DigiTorus86/ESP32-R4ge-Pro/PlatformIO/esp32-r4ge-pro-tombstone/include/boop_wav.h

const PROGMEM unsigned char boop_wav[6360] = {
  0x52, 0x49, 0x46, 0x46, 0xd0, 0x18, 0x00, 0x00, 0x57, 0x41, 0x56, 0x45,
  0x66, 0x6d, 0x74, 0x20, 0x10, 0x00, 0x00, 0x00, 0x01, 0x00, 0x01, 0x00,
  0x11, 0x2b, 0x00, 0x00, 0x22, 0x56, 0x00, 0x00, 0x02, 0x00, 0x10, 0x00,
  0x64, 0x61, 0x74, 0x61, 0xac, 0x18, 0x00, 0x00, 0x01, 0x00, 0xfe, 0xff,
  0x03, 0x00, 0xfb, 0xff, 0x06, 0x00, 0xfa, 0xff, 0x06, 0x00, 0xfb, 0xff,
  0x03, 0x00, 0xfe, 0xff, 0x01, 0x00, 0xff, 0xff, 0x02, 0x00, 0xfe, 0xff,
  0x01, 0x00, 0x00, 0x00, 0xff, 0xff, 0x01, 0x00, 0x00, 0x00, 0xff, 0xff,
  0x02, 0x00, 0xfe, 0xff, 0x01, 0x00, 0x00, 0x00, 0xff, 0xff, 0x02, 0x00,
  0xfe, 0xff, 0x01, 0x00, 0x00, 0x00, 0x00, 0x00, 0xff, 0xff, 0x03, 0x00,
  0xfb, 0xff, 0x05, 0x00, 0xfd, 0xff, 0x00, 0x00, 0x03, 0x00, 0xfb, 0xff,
  0x05, 0x00, 0xfc, 0xff, 0x02, 0x00, 0x00, 0x00, 0xff, 0xff, 0x01, 0x00,
  0xff, 0xff, 0x00, 0x00, 0x02, 0x00, 0xfc, 0xff, 0x05, 0x00, 0xfc, 0xff,
  0x03, 0x00, 0xfd, 0xff, 0x03, 0x00, 0xfc, 0xff, 0x06, 0x00, 0xfa, 0xff,
  0x03, 0x00, 0x00, 0x00, 0xfe, 0xff, 0x03, 0x00, 0xfd, 0xff, 0x02, 0x00,
  0xff, 0xff, 0x01, 0x00, 0xfe, 0xff, 0x03, 0x00, 0xfd, 0xff, 0x03, 0x00,
  0xfc, 0xff, 0x05, 0x00, 0xfb, 0xff, 0x05, 0x00, 0xfb, 0xff, 0x04, 0x00,
  0xfd, 0xff, 0x02, 0x00, 0xff, 0xff, 0x01, 0x00, 0xff, 0xff, 0x01, 0x00,
  0xff, 0xff, 0x00, 0x00, 0x01, 0x00, 0xff, 0xff, 0x00, 0x00, 0x01, 0x00,
  0xff, 0xff, 0x00, 0x00, 0x01, 0x00, 0xfe, 0xff, 0x02, 0x00, 0xff, 0xff,
  0x00, 0x00, 0x00, 0x00, 0x01, 0x00, 0xfe, 0xff, 0x02, 0x00, 0xfe, 0xff,
  0x02, 0x00, 0xfe, 0xff, 0x03, 0x00, 0xfc, 0xff, 0x04, 0x00, 0xfd, 0xff,
  0x01, 0x00, 0x01, 0x00, 0xff, 0xff, 0x00, 0x00, 0x00, 0x00, 0x00, 0x00,
  0x00, 0x00, 0x01, 0x00, 0xfe, 0xff, 0x02, 0x00, 0xfe, 0xff, 0x02, 0x00,
  0xfe, 0xff, 0x03, 0x00, 0xfc, 0xff, 0x04, 0x00, 0xfc, 0xff, 0x04, 0x00,
  0xfd, 0xff, 0x01, 0x00, 0x00, 0x00, 0x00, 0x00, 0x01, 0x00, 0xfe, 0xff,
  0x01, 0x00, 0x00, 0x00, 0x00, 0x00, 0x00, 0x00, 0x00, 0x00, 0xff, 0xff,
  0x02, 0x00, 0xfe, 0xff, 0x02, 0x00, 0xfe, 0xff, 0x02, 0x00, 0xfe, 0xff,
  0x02, 0x00, 0xff, 0xff, 0x00, 0x00, 0x01, 0x00, 0xff, 0xff, 0x00, 0x00,
  0x01, 0x00, 0xfe, 0xff, 0x03, 0x00, 0xfc, 0xff, 0x03, 0x00, 0xff, 0xff,
  0x00, 0x00, 0x01, 0x00, 0xfd, 0xff, 0x03, 0x00, 0xfe, 0xff, 0x02, 0x00,
  0xff, 0xff, 0x00, 0x00, 0xff, 0xff, 0x01, 0x00, 0x00, 0x00, 0x00, 0x00,
  0x00, 0x00, 0xff, 0xff, 0x01, 0x00, 0xff, 0xff, 0x02, 0x00, 0xfe, 0xff,
  0x01, 0x00, 0x00, 0x00, 0x00, 0x00, 0x00, 0x00, 0x00, 0x00, 0x00, 0x00,
  0x00, 0x00, 0x00, 0x00, 0x01, 0x00, 0xfd, 0xff, 0x04, 0x00, 0xfc, 0xff,
  0x04, 0x00, 0xfd, 0xff, 0x01, 0x00, 0x01, 0x00, 0xfe, 0xff, 0x02, 0x00,
  0xff, 0xff, 0x01, 0x00, 0xfe, 0xff, 0x03, 0x00, 0xfc, 0xff, 0x05, 0x00,
  0xfb, 0xff, 0x03, 0x00, 0xff, 0xff, 0x00, 0x00, 0x01, 0x00, 0xff, 0xff,
  0x00, 0x00, 0x00, 0x00, 0x01, 0x00, 0xfe, 0xff, 0x03, 0x00, 0xfd, 0xff,
  0x02, 0x00, 0xfe, 0xff, 0x03, 0x00, 0xfc, 0xff, 0x04, 0x00, 0xfd, 0xff,
  0x02, 0x00, 0xff, 0xff, 0x01, 0x00, 0xfe, 0xff, 0x03, 0x00, 0xfd, 0xff,
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
};
