DigiTorus86/ESP32-R4ge-Pro/PlatformIO/esp32-r4ge-pro-gravitack/include/explosion_wav.h

const PROGMEM unsigned char explosion_wav[5775] = { 
	0x52, 0x49, 0x46, 0x46, 0x87, 0x16, 0x00, 0x00, 0x57, 0x41, 0x56, 0x45,
	0x66, 0x6D, 0x74, 0x20, 0x10, 0x00, 0x00, 0x00, 0x01, 0x00, 0x01, 0x00,
	0x11, 0x2B, 0x00, 0x00, 0x11, 0x2B, 0x00, 0x00, 0x01, 0x00, 0x08, 0x00,
	0x64, 0x61, 0x74, 0x61, 0x63, 0x16, 0x00, 0x00, 0x80, 0x80, 0x80, 0x80,
	0x7F, 0x7E, 0x7D, 0x7C, 0x7B, 0x7B, 0x7A, 0x7A, 0x7D, 0x7F, 0x7F, 0x81,
	0x84, 0x88, 0x8A, 0x88, 0x88, 0x91, 0x9A, 0x9B, 0x9B, 0x9B, 0x9C, 0x9A,
	0x9B, 0x9E, 0xA5, 0xA8, 0xA1, 0x9F, 0xA5, 0xA5, 0x9A, 0x96, 0x93, 0x94,
	0x96, 0x90, 0x8B, 0x84, 0x7C, 0x7A, 0x7B, 0x78, 0x6F, 0x62, 0x54, 0x4D,
	0x4A, 0x4C, 0x51, 0x56, 0x5A, 0x5F, 0x63, 0x68, 0x6E, 0x76, 0x84, 0x96,
	0xA6, 0xB0, 0xB9, 0xC4, 0xD1, 0xD0, 0xCA, 0xC3, 0xBA, 0xB1, 0xA8, 0xA0,
	0x98, 0x92, 0x89, 0x7A, 0x72, 0x77, 0x73, 0x6A, 0x69, 0x60, 0x49, 0x41,
	0x44, 0x44, 0x40, 0x37, 0x33, 0x32, 0x35, 0x3A, 0x3E, 0x47, 0x52, 0x5C,
	0x66, 0x6E, 0x76, 0x7D, 0x84, 0x8D, 0xA4, 0xAF, 0xB4, 0xB8, 0xBC, 0xC8,
	0xCC, 0xCD, 0xD8, 0xF7, 0xFE, 0xF7, 0xFA, 0xF4, 0xE1, 0xD0, 0xC7, 0xCB,
	0xC6, 0xB6, 0xA4, 0x92, 0x83, 0x75, 0x69, 0x5C, 0x4E, 0x3D, 0x29, 0x1A,
	0x0F, 0x08, 0x08, 0x07, 0x07, 0x07, 0x08, 0x0A, 0x1B, 0x30, 0x30, 0x11,
	0x0E, 0x21, 0x20, 0x2F, 0x35, 0x33, 0x3C, 0x43, 0x44, 0x4A, 0x48, 0x45,
	0x46, 0x44, 0x40, 0x43, 0x4F, 0x56, 0x50, 0x44, 0x49, 0x50, 0x54, 0x58,
	0x5F, 0x68, 0x6F, 0x76, 0x7C, 0x86, 0x9A, 0xB2, 0xC0, 0xCE, 0xDF, 0xE4,
	0xE4, 0xE1, 0xDA, 0xD4, 0xCA, 0xBD, 0xB0, 0xA6, 0x9C, 0x93, 0x8C, 0x85,
	0x80, 0x7C, 0x77, 0x74, 0x6F, 0x6B, 0x6A, 0x69, 0x67, 0x66, 0x66, 0x66,
	0x64, 0x5F, 0x5C, 0x5E, 0x5F, 0x52, 0x4B, 0x49, 0x3C, 0x31, 0x36, 0x3B,
	0x3D, 0x47, 0x51, 0x64, 0x7A, 0x85, 0x93, 0xA2, 0xA1, 0x9F, 0xA5, 0xA3,
	0x9F, 0xA9, 0xB1, 0xB2, 0xB6, 0xB5, 0xB7, 0xBB, 0xBE, 0xC8, 0xE1, 0xEE,
	0xE4, 0xE3, 0xE7, 0xEB, 0xF2, 0xFC, 0xFA, 0xEE, 0xE5, 0xD7, 0xBF, 0xB5,
	0xB6, 0xB8, 0xB9, 0xBC, 0xBE, 0xBF, 0xB4, 0xA8, 0x9B, 0x81, 0x87, 0x9D,
	0x97, 0x85, 0x81, 0x80, 0x7D, 0x7C, 0x86, 0x7C, 0x75, 0x7A, 0x73, 0x6A,
	0x62, 0x5C, 0x56, 0x51, 0x4C, 0x49, 0x46, 0x43, 0x40, 0x3C, 0x3D, 0x3D,
	0x37, 0x2B, 0x1C, 0x12, 0x17, 0x1C, 0x0C, 0x09, 0x1C, 0x22, 0x29, 0x31,
	0x3E, 0x45, 0x49, 0x5E, 0x6A, 0x71, 0x74, 0x74, 0x73, 0x81, 0x8E, 0xA6,
	0xC5, 0xBF, 0xC1, 0xC8, 0xCB, 0xC4, 0xB8, 0xB5, 0xBD, 0xBF, 0xBA, 0xB6,
	0xB0, 0xAC, 0xB2, 0xB9, 0xAE, 0xA8, 0xA5, 0xAA, 0xB0, 0xAA, 0x8E, 0x86,
	0x8E, 0x8E, 0x93, 0xA4, 0xAA, 0x9D, 0x7F, 0x58, 0x48, 0x51, 0x5C, 0x59,
	0x61, 0x4F, 0x46, 0x4E, 0x47, 0x41, 0x4B, 0x4A, 0x4D, 0x5E, 0x60, 0x6F,
	0x79, 0x85, 0x93, 0xAB, 0xB8, 0xB9, 0xB1, 0xA8, 0xA8, 0xA6, 0xA6, 0x9E,
	0x9E, 0xA6, 0xA0, 0x96, 0x99, 0x9E, 0xA0, 0xA3, 0xA6, 0x9A, 0x82, 0x6C,
	0x69, 0x74, 0x88, 0xA1, 0xA3, 0x93, 0x74, 0x55, 0x49, 0x4A, 0x66, 0x8F,
	0x9B, 0x70, 0x56, 0x58, 0x5A, 0x57, 0x50, 0x54, 0x5D, 0x6D, 0x78, 0x81,
	0x84, 0x8A, 0x87, 0x90, 0x92, 0x8C, 0x91, 0x9B, 0xAC, 0xA9, 0x9E, 0xA3,
	0xA5, 0xA4, 0xAB, 0xBC, 0xC8, 0xC1, 0xAF, 0xAF, 0xB6, 0x97, 0x9E, 0xAC,
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
};
