DigiTorus86/ESP32-R4ge-Pro/PlatformIO/esp32-r4ge-pro-gravitack/include/fire_wav.h

const PROGMEM unsigned char fire_wav[3431] = { 
	0x52, 0x49, 0x46, 0x46, 0x5F, 0x0D, 0x00, 0x00, 0x57, 0x41, 0x56, 0x45,
	0x66, 0x6D, 0x74, 0x20, 0x10, 0x00, 0x00, 0x00, 0x01, 0x00, 0x01, 0x00,
	0x11, 0x2B, 0x00, 0x00, 0x11, 0x2B, 0x00, 0x00, 0x01, 0x00, 0x08, 0x00,
	0x64, 0x61, 0x74, 0x61, 0x3B, 0x0D, 0x00, 0x00, 0x7F, 0x80, 0x7F, 0x80,
	0x7E, 0x81, 0x7D, 0x7F, 0x7E, 0x83, 0x84, 0x95, 0x96, 0x76, 0x68, 0x60,
	0x6A, 0x67, 0x76, 0x71, 0x85, 0x7D, 0xA2, 0x95, 0x7B, 0x94, 0x90, 0xBE,
	0x92, 0x91, 0xC1, 0xA3, 0x96, 0x7B, 0x8D, 0xAA, 0x7D, 0x78, 0x60, 0x8A,
	0x77, 0x46, 0x41, 0x4A, 0x76, 0x36, 0x36, 0x43, 0x70, 0x80, 0x49, 0x51,
	0x69, 0x82, 0x68, 0x5A, 0x5C, 0xA3, 0x92, 0x9D, 0xAA, 0x84, 0xD1, 0xA2,
	0x97, 0xC3, 0x92, 0x96, 0xA8, 0x8A, 0xAC, 0xCF, 0xCB, 0xA2, 0xA0, 0x97,
	0xC6, 0xC3, 0xAF, 0xB2, 0x9D, 0xD3, 0x9B, 0x6A, 0x73, 0x70, 0x58, 0x79,
	0x63, 0x41, 0x5D, 0x74, 0x57, 0x23, 0x12, 0x29, 0x46, 0x3E, 0x55, 0x5A,
	0x52, 0x5F, 0x6C, 0x38, 0x34, 0x40, 0x87, 0xA0, 0x6D, 0x82, 0x7E, 0xB5,
	0xB8, 0x7F, 0x8E, 0xA8, 0x84, 0x9C, 0xBE, 0xB2, 0x93, 0xA0, 0xCC, 0xC8,
	0xC5, 0x95, 0x97, 0xA5, 0xAA, 0x6E, 0x7A, 0xB0, 0x9F, 0xB7, 0x92, 0x85,
	0x77, 0x5F, 0x5E, 0x4D, 0x7D, 0x78, 0x74, 0x85, 0xA3, 0xAA, 0x39, 0x22,
	0x37, 0x53, 0x63, 0x78, 0x7B, 0x9B, 0x8B, 0x29, 0x50, 0x62, 0x4D, 0x3F,
	0x58, 0x8D, 0x93, 0x94, 0x76, 0x7C, 0x77, 0x5B, 0x67, 0x6E, 0xA5, 0x80,
	0x87, 0x96, 0xA7, 0x82, 0x55, 0x82, 0x80, 0x75, 0x99, 0xCC, 0x96, 0x82,
	0x72, 0x95, 0x72, 0x82, 0xA6, 0xAA, 0x83, 0x94, 0xA5, 0x9C, 0xA0, 0x79,
	0x8B, 0x5E, 0x8D, 0x9B, 0xB2, 0x9D, 0x96, 0x62, 0x7A, 0x8C, 0x56, 0x76,
	0x84, 0x82, 0x78, 0xA6, 0x8B, 0xB1, 0x92, 0x72, 0x77, 0x76, 0x89, 0xA5,
	0xDA, 0xAA, 0x91, 0x8E, 0x68, 0x70, 0x90, 0xC3, 0xC0, 0x97, 0x7D, 0x74,
	0x7D, 0x7A, 0x80, 0x7C, 0x88, 0x5A, 0x5D, 0x71, 0x70, 0x96, 0x6D, 0x65,
	0x72, 0x4D, 0x5C, 0x56, 0x80, 0x74, 0x5D, 0x60, 0x33, 0x4F, 0x51, 0x5E,
	0x55, 0x67, 0x6D, 0x55, 0x69, 0x73, 0x82, 0x9D, 0x91, 0x79, 0x71, 0x85,
	0x68, 0x57, 0x74, 0x89, 0x7B, 0x6F, 0x7C, 0x7B, 0xA1, 0xAD, 0xAF, 0xA7,
	0xAB, 0x9D, 0x91, 0x9A, 0xA1, 0xA8, 0xBB, 0xB2, 0x90, 0x97, 0x88, 0x86,
	0x92, 0x7B, 0x87, 0x76, 0x67, 0x6B, 0x55, 0x69, 0x79, 0x6B, 0x59, 0x64,
	0x67, 0x58, 0x5D, 0x5E, 0x69, 0x70, 0x80, 0x93, 0x71, 0x7F, 0x75, 0x92,
	0x86, 0x82, 0x91, 0xA6, 0xB6, 0x92, 0xA1, 0x7D, 0x79, 0x8B, 0x8C, 0x83,
	0x90, 0x76, 0x80, 0x6D, 0x67, 0x6C, 0x64, 0x75, 0x88, 0x89, 0x6D, 0x7E,
	0x76, 0x88, 0x77, 0x69, 0x76, 0x8B, 0x9D, 0x97, 0xA8, 0xA9, 0xA0, 0xA1,
	0x9E, 0x96, 0xAE, 0x9C, 0x8A, 0xAE, 0x94, 0x8B, 0x90, 0x9D, 0x99, 0x9D,
	0xA1, 0x98, 0x80, 0x72, 0x74, 0x72, 0x67, 0x65, 0x7E, 0x7F, 0x81, 0x66,
	0x7B, 0x7F, 0x74, 0x67, 0x5F, 0x6A, 0x68, 0x6B, 0x59, 0x4C, 0x60, 0x4D,
	0x59, 0x4D, 0x5D, 0x62, 0x78, 0x76, 0x6F, 0x68, 0x68, 0x74, 0x50, 0x6D,
	0x49, 0x60, 0x64, 0x7E, 0x68, 0x79, 0x74, 0x65, 0x84, 0x6B, 0x86, 0x75,
	0x9D, 0x7B, 0x74, 0x87, 0x7B, 0x9C, 0x7D, 0xB5, 0x90, 0xBC, 0x9A, 0x97,
	0x97, 0x91, 0xA7, 0x7D, 0xBA, 0x88, 0xCD, 0x8C, 0xDA, 0xAA, 0xDC, 0xAB,
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
};
