DigiTorus86/ESP32-R4ge-Pro/PlatformIO/esp32-r4ge-pro-gravitack/include/refuel_wav.h

const PROGMEM unsigned char refuel_wav[6324] = { 
	0x52, 0x49, 0x46, 0x46, 0xAC, 0x18, 0x00, 0x00, 0x57, 0x41, 0x56, 0x45,
	0x66, 0x6D, 0x74, 0x20, 0x10, 0x00, 0x00, 0x00, 0x01, 0x00, 0x01, 0x00,
	0x11, 0x2B, 0x00, 0x00, 0x11, 0x2B, 0x00, 0x00, 0x01, 0x00, 0x08, 0x00,
	0x64, 0x61, 0x74, 0x61, 0x88, 0x18, 0x00, 0x00, 0x80, 0x80, 0x7F, 0x7F,
	0x7F, 0x7F, 0x7F, 0x7F, 0x7F, 0x7F, 0x7F, 0x7F, 0x80, 0x81, 0x81, 0x81,
	0x81, 0x80, 0x80, 0x7F, 0x7F, 0x7E, 0x7E, 0x7E, 0x7E, 0x7E, 0x7E, 0x7E,
	0x7E, 0x7E, 0x7E, 0x7E, 0x7F, 0x80, 0x81, 0x81, 0x80, 0x80, 0x7E, 0x7E,
	0x7D, 0x7D, 0x7D, 0x7D, 0x7D, 0x7D, 0x7D, 0x7F, 0x81, 0x7F, 0x7E, 0x7F,
	0x80, 0x7E, 0x7E, 0x80, 0x82, 0x80, 0x80, 0x81, 0x82, 0x80, 0x7F, 0x80,
	0x80, 0x7F, 0x81, 0x80, 0x7E, 0x7E, 0x7F, 0x7F, 0x7D, 0x7E, 0x80, 0x81,
	0x7F, 0x7F, 0x81, 0x80, 0x7E, 0x7F, 0x82, 0x84, 0x85, 0x85, 0x86, 0x85,
	0x84, 0x81, 0x7E, 0x7D, 0x7D, 0x7F, 0x81, 0x84, 0x86, 0x87, 0x85, 0x84,
	0x82, 0x81, 0x80, 0x80, 0x80, 0x81, 0x81, 0x83, 0x84, 0x86, 0x87, 0x88,
	0x87, 0x84, 0x82, 0x7F, 0x7D, 0x7C, 0x7C, 0x7D, 0x7F, 0x80, 0x81, 0x82,
	0x82, 0x82, 0x81, 0x80, 0x7F, 0x7D, 0x7C, 0x7A, 0x79, 0x79, 0x7A, 0x7C,
	0x7E, 0x81, 0x83, 0x85, 0x84, 0x84, 0x83, 0x82, 0x82, 0x81, 0x81, 0x82,
	0x84, 0x85, 0x86, 0x86, 0x85, 0x83, 0x80, 0x7D, 0x7B, 0x7A, 0x7A, 0x7B,
	0x7C, 0x7C, 0x7B, 0x7A, 0x78, 0x77, 0x7A, 0x80, 0x7F, 0x79, 0x7A, 0x7F,
	0x7B, 0x79, 0x7E, 0x83, 0x82, 0x80, 0x82, 0x84, 0x7E, 0x7B, 0x7E, 0x7E,
	0x7D, 0x7F, 0x7D, 0x78, 0x77, 0x77, 0x77, 0x78, 0x7D, 0x7F, 0x7B, 0x7B,
	0x7D, 0x7A, 0x79, 0x7E, 0x83, 0x83, 0x7F, 0x7E, 0x7F, 0x83, 0x86, 0x88,
	0x84, 0x7F, 0x7A, 0x77, 0x76, 0x78, 0x7B, 0x7F, 0x82, 0x85, 0x88, 0x89,
	0x89, 0x88, 0x87, 0x85, 0x82, 0x7F, 0x7D, 0x7A, 0x78, 0x77, 0x7A, 0x7F,
	0x85, 0x8A, 0x8D, 0x8B, 0x87, 0x82, 0x7E, 0x7C, 0x7B, 0x7A, 0x7A, 0x7A,
	0x7B, 0x7E, 0x82, 0x88, 0x8C, 0x8E, 0x8D, 0x8A, 0x85, 0x81, 0x7E, 0x7B,
	0x78, 0x77, 0x76, 0x75, 0x74, 0x74, 0x75, 0x77, 0x7A, 0x7E, 0x85, 0x89,
	0x89, 0x85, 0x7F, 0x78, 0x73, 0x70, 0x70, 0x70, 0x71, 0x71, 0x72, 0x7A,
	0x82, 0x7E, 0x76, 0x7B, 0x7E, 0x77, 0x78, 0x82, 0x85, 0x80, 0x7E, 0x86,
	0x86, 0x7C, 0x7B, 0x7F, 0x7C, 0x81, 0x80, 0x77, 0x76, 0x7A, 0x7A, 0x75,
	0x75, 0x81, 0x83, 0x7A, 0x7D, 0x82, 0x79, 0x74, 0x7C, 0x89, 0x91, 0x93,
	0x93, 0x92, 0x8B, 0x82, 0x7B, 0x75, 0x76, 0x7D, 0x87, 0x92, 0x98, 0x97,
	0x93, 0x8D, 0x87, 0x84, 0x83, 0x82, 0x84, 0x86, 0x89, 0x8D, 0x93, 0x9A,
	0x9D, 0x9B, 0x93, 0x8A, 0x82, 0x7B, 0x77, 0x75, 0x76, 0x79, 0x7D, 0x80,
	0x82, 0x82, 0x81, 0x7E, 0x7A, 0x76, 0x71, 0x6D, 0x6A, 0x6A, 0x6E, 0x75,
	0x7D, 0x86, 0x8E, 0x92, 0x94, 0x92, 0x90, 0x8F, 0x8F, 0x92, 0x95, 0x99,
	0x9C, 0x9B, 0x96, 0x8D, 0x83, 0x7B, 0x75, 0x70, 0x71, 0x73, 0x75, 0x76,
	0x74, 0x70, 0x69, 0x6A, 0x7B, 0x85, 0x77, 0x70, 0x7D, 0x79, 0x6F, 0x7A,
	0x87, 0x84, 0x7E, 0x84, 0x8B, 0x7E, 0x72, 0x7B, 0x78, 0x76, 0x7F, 0x76,
	0x67, 0x68, 0x6A, 0x66, 0x67, 0x79, 0x7F, 0x71, 0x73, 0x7B, 0x70, 0x6A,
	0x7B, 0x8C, 0x8D, 0x84, 0x80, 0x83, 0x8C, 0x96, 0x97, 0x8D, 0x7F, 0x73,
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
};
