DigiTorus86/ESP32-R4ge-Pro/PlatformIO/esp32-r4ge-pro-tombstone/include/explosion_wav.h

const PROGMEM uint8_t explosion_wav[22450] = {
0x52, 0x49, 0x46, 0x46, 0xAA, 0x57, 0x00, 0x00, 
0x57, 0x41, 0x56, 0x45, 0x66, 0x6D, 0x74, 0x20, 
0x10, 0x00, 0x00, 0x00, 0x01, 0x00, 0x01, 0x00, 
0x11, 0x2B, 0x00, 0x00, 0x22, 0x56, 0x00, 0x00, 
0x02, 0x00, 0x10, 0x00, 0x64, 0x61, 0x74, 0x61, 
0x86, 0x57, 0x00, 0x00, 0x01, 0x00, 0xFE, 0xFF, 
0x02, 0x00, 0xFE, 0xFF, 0x01, 0x00, 0xFF, 0xFF, 
0x03, 0x00, 0xFB, 0xFF, 0x06, 0x00, 0xFA, 0xFF, 
0x06, 0x00, 0xFD, 0xFF, 0x01, 0x00, 0xFE, 0xFF, 
0x02, 0x00, 0xFD, 0xFF, 0x04, 0x00, 0xFC, 0xFF, 
0x01, 0x00, 0xFF, 0xFF, 0xFF, 0xFF, 0x00, 0x00, 
0x00, 0x00, 0x00, 0x00, 0xFD, 0xFF, 0x04, 0x00, 
0xFC, 0xFF, 0x04, 0x00, 0xFD, 0xFF, 0x04, 0x00, 
0x00, 0x00, 0x03, 0x00, 0x00, 0x00, 0x02, 0x00, 
0xFD, 0xFF, 0x04, 0x00, 0xFE, 0xFF, 0xFE, 0xFF, 
0xFF, 0xFF, 0xFC, 0xFF, 0x00, 0x00, 0x03, 0x00, 
0xFF, 0xFF, 0x03, 0x00, 0xFE, 0xFF, 0xFF, 0xFF, 
0xFD, 0xFF, 0x05, 0x00, 0xFC, 0xFF, 0x03, 0x00, 
0xF9, 0xFF, 0x09, 0x00, 0xFA, 0xFF, 0x05, 0x00, 
0xFA, 0xFF, 0x09, 0x00, 0xF9, 0xFF, 0x0D, 0x00, 
0xFA, 0xFF, 0x08, 0x00, 0xF5, 0xFF, 0x11, 0x00, 
0xF9, 0xFF, 0x0D, 0x00, 0xEE, 0xFF, 0x0E, 0x00, 
0xF4, 0xFF, 0x13, 0x00, 0x02, 0x00, 0x04, 0x00, 
0x02, 0x00, 0xFB, 0xFF, 0x00, 0x00, 0xFB, 0xFF, 
0x0B, 0x00, 0xE8, 0xFF, 0x21, 0x00, 0xDD, 0xFF, 
0x32, 0x00, 0xD2, 0xFF, 0x48, 0x00, 0xC9, 0xFF, 
0x4F, 0x00, 0xBA, 0xFF, 0x4E, 0x00, 0xB5, 0xFF, 
0x4E, 0x00, 0xB2, 0xFF, 0x42, 0x00, 0xB8, 0xFF, 
0x39, 0x00, 0xCE, 0xFF, 0x20, 0x00, 0xE5, 0xFF, 
0xF8, 0xFF, 0x29, 0x00, 0xE8, 0xFF, 0x94, 0x10, 
0x25, 0x14, 0x51, 0x13, 0x60, 0x13, 0xE2, 0x13, 
0xB9, 0x12, 0x23, 0x15, 0xD9, 0x0B, 0x8A, 0xFE, 
0xA2, 0x00, 0xB0, 0xFF, 0x0B, 0x00, 0x1D, 0x00, 
0xD4, 0xFF, 0x5C, 0x00, 0x99, 0xFF, 0x25, 0x01, 
0x84, 0x10, 0xF9, 0x14, 0x29, 0x12, 0x43, 0x15, 
0x97, 0x0E, 0x22, 0x00, 0xE4, 0xFF, 0x5D, 0x00, 
0xC0, 0xFF, 0x41, 0x00, 0xB1, 0xFF, 0x34, 0x00, 
0xBF, 0xFF, 0x1B, 0x00, 0xFF, 0xFF, 0xE6, 0xFF, 
0x6A, 0x00, 0xC3, 0xFF, 0x20, 0x02, 0xD2, 0x11, 
0x4A, 0x14, 0xA5, 0x12, 0x5A, 0x15, 0xB9, 0x0D, 
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
