DigiTorus86/ESP32-R4ge-Pro/PlatformIO/esp32-r4ge-pro-tombstone/include/fire_wav.h

const PROGMEM unsigned char fire_wav[6416] = {
0x52, 0x49, 0x46, 0x46, 0x08, 0x19, 0x00, 0x00, 
0x57, 0x41, 0x56, 0x45, 0x66, 0x6D, 0x74, 0x20, 
0x10, 0x00, 0x00, 0x00, 0x01, 0x00, 0x01, 0x00, 
0x11, 0x2B, 0x00, 0x00, 0x22, 0x56, 0x00, 0x00, 
0x02, 0x00, 0x10, 0x00, 0x64, 0x61, 0x74, 0x61, 
0xE4, 0x18, 0x00, 0x00, 0x0A, 0x00, 0xF5, 0xFF, 
0x0B, 0x00, 0xF7, 0xFF, 0x0B, 0x00, 0xF6, 0xFF, 
0x08, 0x00, 0xF6, 0xFF, 0x06, 0x00, 0xF8, 0xFF, 
0x02, 0x00, 0x00, 0x00, 0x02, 0x00, 0x16, 0x00, 
0xF9, 0xFF, 0x08, 0x00, 0x07, 0x00, 0x19, 0x00, 
0xEE, 0xFF, 0x24, 0x00, 0xDD, 0xFF, 0x28, 0x00, 
0xC3, 0xFF, 0x29, 0x00, 0x0D, 0x00, 0x23, 0x00, 
0xB2, 0xFF, 0x5E, 0x00, 0xDB, 0xFF, 0x3B, 0x00, 
0xEE, 0xFF, 0xC7, 0xFF, 0xEF, 0xFF, 0xC0, 0xFF, 
0x7A, 0xFF, 0x07, 0x00, 0xC3, 0xFF, 0xF2, 0xFF, 
0x63, 0x00, 0x14, 0xFF, 0xC1, 0x00, 0xDD, 0xFE, 
0x3D, 0x0C, 0x9B, 0x14, 0xE0, 0x12, 0x38, 0x14, 
0xC6, 0x13, 0xA6, 0x14, 0xE4, 0x15, 0x1A, 0x16, 
0x01, 0x16, 0x9C, 0x16, 0x0C, 0x19, 0xCA, 0x17, 
0xE1, 0x19, 0x15, 0x18, 0xC6, 0x1A, 0x79, 0x15, 
0xA4, 0x00, 0xE5, 0xFF, 0x3C, 0x00, 0x87, 0xFF, 
0x7A, 0x01, 0xA1, 0x00, 0xA9, 0x00, 0x3D, 0x00, 
0xB5, 0xFE, 0xFD, 0x11, 0x9B, 0x20, 0x84, 0x1C, 
0xDC, 0x1F, 0x63, 0x1E, 0x10, 0x05, 0xF7, 0xFC, 
0x24, 0x01, 0x58, 0xFF, 0xF6, 0x01, 0xEB, 0x00, 
0x68, 0x01, 0x4B, 0x00, 0xC5, 0xFF, 0xBD, 0xFE, 
0xD3, 0x00, 0x69, 0x00, 0x70, 0x02, 0x4A, 0x00, 
0x35, 0x16, 0x57, 0x25, 0xA7, 0x1D, 0xF8, 0x21, 
0x1F, 0x1C, 0xCA, 0x03, 0x4B, 0xFC, 0x26, 0x03, 
0x76, 0xFB, 0xAA, 0x0A, 0xB1, 0x20, 0x5A, 0x21, 
0x50, 0x1E, 0x75, 0x23, 0xDE, 0x0F, 0x89, 0xFD, 
0x10, 0x02, 0xA0, 0x00, 0xB3, 0x00, 0x21, 0x00, 
0xB1, 0x01, 0x13, 0x00, 0x70, 0x00, 0x68, 0xFF, 
0xB9, 0x00, 0x50, 0x00, 0x05, 0x02, 0xA9, 0xFE, 
0x5F, 0x0B, 0x68, 0x22, 0x6E, 0x20, 0xCF, 0x1F, 
0x76, 0x22, 0x31, 0x0E, 0xAD, 0xFB, 0x27, 0x02, 
0xF7, 0xFD, 0x0B, 0x02, 0xF8, 0x18, 0xE1, 0x22, 
0x02, 0x1E, 0x48, 0x25, 0x3A, 0x1B, 0xC6, 0x02, 
0x94, 0xFF, 0xE4, 0x02, 0xF9, 0xFB, 0x9D, 0x0D, 
0x05, 0x23, 0x68, 0x20, 0x88, 0x21, 0x89, 0x20, 
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
};
