DigiTorus86/ESP32-R4ge-Pro/ArduinoIDE/esp32-r4ge-pro-drummer/Icons.h

/* Image include file for RGB565 bitmap 
 * Original filename: sdcard24.png
 * Width: 18 * Height: 24
 */

const PROGMEM uint16_t sd_icon[432] = {
0x000000, 0x000000, 0x000000, 0x000000, 0x000000, 0x000000, 0x000000, 0x000000, // 8 pixels
0x000000, 0x000000, 0x000000, 0x000000, 0x000000, 0x000000, 0x000000, 0x000000, // 16 pixels
0x000000, 0x000000, 0x000000, 0x000000, 0x000000, 0x000000, 0x000000, 0x0022B0, // 24 pixels
0x0022B0, 0x0022B0, 0x0022B0, 0x0022B0, 0x0022B0, 0x0022B0, 0x0022B0, 0x0022B0, // 32 pixels
0x0022B0, 0x0022B0, 0x0022B0, 0x000000, 0x000000, 0x000000, 0x000000, 0x000000, // 40 pixels
0x0022B0, 0x009541, 0x009541, 0x0022B0, 0x009541, 0x009541, 0x0022B0, 0x009541, // 48 pixels
0x009541, 0x0022B0, 0x009541, 0x009541, 0x0022B0, 0x000000, 0x000000, 0x000000, // 56 pixels
0x000000, 0x0022B0, 0x0022B0, 0x009541, 0x009541, 0x0022B0, 0x009541, 0x009541, // 64 pixels
0x0022B0, 0x009541, 0x009541, 0x0022B0, 0x009541, 0x009541, 0x0022B0, 0x000000, // 72 pixels
0x000000, 0x000000, 0x0022B0, 0x0022B0, 0x0022B0, 0x009541, 0x009541, 0x0022B0, // 80 pixels
0x009541, 0x009541, 0x0022B0, 0x009541, 0x009541, 0x0022B0, 0x009541, 0x009541, // 88 pixels
0x0022B0, 0x000000, 0x000000, 0x0022B0, 0x009541, 0x009541, 0x0022B0, 0x0022B0, // 96 pixels
0x0022B0, 0x0022B0, 0x0022B0, 0x0022B0, 0x0022B0, 0x0022B0, 0x0022B0, 0x0022B0, // 104 pixels
0x0022B0, 0x0022B0, 0x0022B0, 0x000000, 0x000000, 0x0022B0, 0x009541, 0x009541, // 112 pixels
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
0x000000, 0x000000, 0x000000, 0x000000, 0x002124, 0x00632C, 0x009492, 0x00C638, // 936 pixels
0x00DEDB, 0x00F7BE, 0x00F7BE, 0x00F79E, 0x00EF7D, 0x00EF7D, 0x00EF7D, 0x00EF7D, // 944 pixels
0x00EF7D, 0x00EF7D, 0x00EF7D, 0x00EF7D, 0x00F79E, 0x00F7BE, 0x00F7BE, 0x00DEDB, // 952 pixels
0x00C638, 0x009492, 0x00632C, 0x002124, 0x000000, 0x000000, 0x000000, 0x000000, // 960 pixels
};
