DigiTorus86/ESP32-R4ge-Pro/ArduinoIDE/esp32-r4ge-pro-drummer/Kit01_chat_wav.h

/* Include file for 8-bit PCM audio data 
 * Original filename: Kit01_chat.wav
 * Samples: 11026
 */

const PROGMEM uint8_t Kit01_chat_wav[11026] = {
0x52, 0x49, 0x46, 0x46, 0x0A, 0x2B, 0x00, 0x00, 
0x57, 0x41, 0x56, 0x45, 0x66, 0x6D, 0x74, 0x20, 
0x10, 0x00, 0x00, 0x00, 0x01, 0x00, 0x01, 0x00, 
0x22, 0x56, 0x00, 0x00, 0x44, 0xAC, 0x00, 0x00, 
0x02, 0x00, 0x10, 0x00, 0x64, 0x61, 0x74, 0x61, 
0xE6, 0x2A, 0x00, 0x00, 0x96, 0x00, 0x69, 0xFF, 
0x2C, 0x00, 0x7F, 0xF4, 0xF4, 0xEF, 0x99, 0x07, 
0xAB, 0x09, 0x2D, 0x02, 0x0C, 0x0D, 0x31, 0x0D, 
0x5F, 0x0D, 0x02, 0x0D, 0x70, 0x12, 0x6C, 0x19, 
0x66, 0x16, 0xF6, 0x17, 0x61, 0x1F, 0x96, 0x16, 
0xF2, 0x1F, 0xAD, 0x33, 0x5C, 0x0C, 0xEC, 0xF9, 
0x8E, 0x1C, 0xA5, 0x1A, 0xA6, 0x1E, 0x4D, 0x21, 
0xD3, 0x16, 0xFD, 0x17, 0x3C, 0x01, 0xB2, 0x03, 
0xFB, 0xFB, 0x96, 0xFC, 0x0F, 0xF9, 0xF9, 0xF6, 
0x9B, 0xE5, 0x04, 0xF4, 0xA0, 0xEE, 0xD3, 0xD6, 
0x7E, 0xE9, 0x7B, 0xE7, 0x24, 0xED, 0xB0, 0xED, 
0x38, 0xF1, 0xAA, 0xF2, 0x1C, 0xF6, 0xE8, 0xEE, 
0x8C, 0xE5, 0xDD, 0xE5, 0x12, 0xFF, 0x0C, 0xE7, 
0x2C, 0xE7, 0x62, 0xE9, 0xDF, 0x04, 0xA8, 0xCF, 
0x67, 0xE8, 0x51, 0x0D, 0x12, 0xD6, 0xDA, 0x0C, 
0xE0, 0xE9, 0x83, 0xF8, 0xE0, 0xF0, 0xEB, 0xEC, 
0x06, 0xF3, 0x56, 0xEA, 0xBB, 0xFA, 0xA2, 0xDC, 
0x51, 0xEF, 0x1B, 0xF0, 0x4C, 0xDA, 0x1E, 0x02, 
0x36, 0xE6, 0xBF, 0xE7, 0x76, 0xFB, 0xCD, 0xE0, 
0xD6, 0x00, 0xB7, 0xF8, 0x2B, 0xFA, 0xAB, 0xEB, 
0x50, 0xEC, 0x6A, 0x09, 0xBF, 0xF5, 0xB3, 0xF3, 
0x54, 0xF3, 0x15, 0x04, 0x14, 0xEC, 0x39, 0xF7, 
0xD6, 0x20, 0x4C, 0xF5, 0x5F, 0xFC, 0xA0, 0x08, 
0x63, 0xFE, 0x6E, 0x0B, 0x82, 0x09, 0x01, 0x01, 
0xA8, 0x09, 0x3B, 0xFA, 0x12, 0x20, 0xB2, 0x07, 
0x0E, 0x00, 0x9B, 0x14, 0x32, 0x05, 0x9D, 0x14, 
0x74, 0x0F, 0x19, 0x12, 0x25, 0x0D, 0x3A, 0x1C, 
0xB3, 0x05, 0xAF, 0x16, 0x4B, 0x06, 0x1B, 0x17, 
0x99, 0x1D, 0x2C, 0x0F, 0x84, 0x12, 0x84, 0x12, 
0xD7, 0x0E, 0xB6, 0xFF, 0xDA, 0x10, 0xF3, 0x01, 
0xCA, 0x19, 0xE8, 0x19, 0xD3, 0x16, 0x89, 0x02, 
0x16, 0x00, 0x39, 0x05, 0x0D, 0x07, 0x12, 0xF4, 
0x04, 0xF3, 0x46, 0x04, 0xFC, 0xF3, 0x17, 0xFF, 
0xEE, 0xF2, 0xB7, 0xFE, 0xC6, 0xF5, 0xE7, 0xFB, 
0xE3, 0xF7, 0xFD, 0x0F, 0x16, 0x18, 0x04, 0xF4, 
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
