DigiTorus86/ESP32-R4ge-Pro/ArduinoIDE/esp32-r4ge-pro-drummer/Kit01_kick_wav.h

/* Include file for 8-bit PCM audio data 
 * Original filename: Kit01_kick.wav
 * Samples: 12056
 */

const PROGMEM uint8_t Kit01_kick_wav[12056] = {
0x52, 0x49, 0x46, 0x46, 0x10, 0x2F, 0x00, 0x00, 
0x57, 0x41, 0x56, 0x45, 0x66, 0x6D, 0x74, 0x20, 
0x10, 0x00, 0x00, 0x00, 0x01, 0x00, 0x01, 0x00, 
0x22, 0x56, 0x00, 0x00, 0x44, 0xAC, 0x00, 0x00, 
0x02, 0x00, 0x10, 0x00, 0x64, 0x61, 0x74, 0x61, 
0xEC, 0x2E, 0x00, 0x00, 0x19, 0x00, 0xD5, 0xFE, 
0xD9, 0xFD, 0x6B, 0xFE, 0x76, 0xFE, 0x47, 0xFE, 
0xD7, 0xFD, 0xF2, 0xFC, 0xC5, 0xFB, 0x6B, 0xFA, 
0x83, 0xF9, 0xEE, 0xF9, 0xFA, 0xF9, 0x5A, 0xF9, 
0x79, 0xF8, 0x11, 0xF7, 0xE8, 0xF4, 0xE2, 0xF1, 
0xCF, 0xEE, 0x39, 0xEC, 0x49, 0xE9, 0x4E, 0xE6, 
0xD4, 0xE3, 0x62, 0xE1, 0x35, 0xDF, 0x9C, 0xDC, 
0x1E, 0xDA, 0xE9, 0xD7, 0x5F, 0xD5, 0x4C, 0xD2, 
0xCC, 0xCF, 0x8A, 0xCD, 0x97, 0xCB, 0xEF, 0xC9, 
0x92, 0xC8, 0xE3, 0xC7, 0xFA, 0xC6, 0x71, 0xC6, 
0x30, 0xC6, 0xC0, 0xC5, 0x47, 0xC5, 0x20, 0xC5, 
0x09, 0xC5, 0x47, 0xC5, 0x1D, 0xC6, 0xFB, 0xC6, 
0xE1, 0xC7, 0x29, 0xC9, 0x61, 0xCB, 0x17, 0xCE, 
0x9F, 0xD1, 0x54, 0xD5, 0xC7, 0xD8, 0x14, 0xDC, 
0x11, 0xDF, 0xEF, 0xE1, 0x60, 0xE5, 0xE7, 0xE8, 
0x6A, 0xEB, 0x95, 0xED, 0x3B, 0xEF, 0xD5, 0xF0, 
0x1B, 0xF2, 0x37, 0xF2, 0x7A, 0xF1, 0x4A, 0xF0, 
0x07, 0xF0, 0x56, 0xF2, 0x99, 0xF6, 0x05, 0xFC, 
0xFE, 0x01, 0x5A, 0x06, 0x9E, 0x08, 0x11, 0x09, 
0xCA, 0x08, 0x0D, 0x09, 0x92, 0x08, 0x95, 0x05, 
0x8D, 0x06, 0xC0, 0x0A, 0x51, 0x0E, 0x1E, 0x12, 
0xBF, 0x10, 0x6B, 0x0E, 0x20, 0x12, 0xA0, 0x16, 
0xCA, 0x1D, 0x30, 0x27, 0x70, 0x2B, 0xCA, 0x32, 
0x85, 0x39, 0xE0, 0x3E, 0x42, 0x45, 0x28, 0x4D, 
0x8C, 0x5A, 0x28, 0x66, 0x28, 0x71, 0xD7, 0x77, 
0xE6, 0x7C, 0xFD, 0x7F, 0xD6, 0x7F, 0xFD, 0x7F, 
0xFF, 0x7F, 0x04, 0x7F, 0x0E, 0x7B, 0x9F, 0x7B, 
0x61, 0x7F, 0xF9, 0x7F, 0xDC, 0x7F, 0xFD, 0x7F, 
0xD9, 0x7F, 0x6A, 0x7F, 0xDC, 0x76, 0x85, 0x6F, 
0xAE, 0x6F, 0x2D, 0x73, 0x9F, 0x7B, 0xD7, 0x7F, 
0xFC, 0x7F, 0xEC, 0x7F, 0xFD, 0x7F, 0x1F, 0x7F, 
0x98, 0x7E, 0x4C, 0x7D, 0xB7, 0x7A, 0xF4, 0x77, 
0x5A, 0x74, 0x63, 0x71, 0xB4, 0x6A, 0xD8, 0x64, 
0xD9, 0x5D, 0x90, 0x54, 0xD6, 0x49, 0x39, 0x3B, 
0xE6, 0x30, 0xD8, 0x2A, 0xA0, 0x28, 0xE9, 0x27, 
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
};
