DigiTorus86/ESP32-R4ge-Pro/ArduinoIDE/esp32-r4ge-pro-drummer/Kit01_ohat_wav.h

/* Include file for 8-bit PCM audio data 
 * Original filename: Kit01_ohat.wav
 * Samples: 33474
 */

const PROGMEM uint8_t Kit01_ohat_wav[33474] = {
0x52, 0x49, 0x46, 0x46, 0xBA, 0x82, 0x00, 0x00, 
0x57, 0x41, 0x56, 0x45, 0x66, 0x6D, 0x74, 0x20, 
0x10, 0x00, 0x00, 0x00, 0x01, 0x00, 0x01, 0x00, 
0x22, 0x56, 0x00, 0x00, 0x44, 0xAC, 0x00, 0x00, 
0x02, 0x00, 0x10, 0x00, 0x64, 0x61, 0x74, 0x61, 
0x96, 0x82, 0x00, 0x00, 0xE9, 0x00, 0x4E, 0xFF, 
0x32, 0x02, 0x54, 0xF7, 0xBC, 0xE7, 0x3F, 0x0B, 
0x5A, 0x0A, 0x52, 0xFE, 0x27, 0x12, 0x33, 0x0E, 
0x60, 0x0D, 0xA7, 0x10, 0x6F, 0x14, 0xB4, 0x19, 
0xB7, 0x1B, 0x5A, 0x19, 0x2A, 0x22, 0xBD, 0x1F, 
0xC0, 0x14, 0x10, 0x2D, 0x57, 0x1F, 0x0B, 0x00, 
0xF2, 0x14, 0x08, 0x23, 0x19, 0x19, 0xEC, 0x1F, 
0x3E, 0x16, 0x64, 0x09, 0xFC, 0x03, 0xED, 0x03, 
0x6D, 0xF9, 0x93, 0xF0, 0x8D, 0xF3, 0x23, 0xFA, 
0x9F, 0xEA, 0x84, 0xE2, 0xCB, 0xEF, 0x64, 0xDE, 
0xA6, 0xDB, 0x78, 0xE8, 0x47, 0xE7, 0x84, 0xEC, 
0xDB, 0xEB, 0x6E, 0xE2, 0x2D, 0xF3, 0x62, 0xE3, 
0x33, 0xE0, 0x73, 0xE8, 0x2C, 0xEB, 0x00, 0xE2, 
0xA9, 0xEF, 0xF5, 0xE9, 0xEC, 0xF9, 0xCA, 0xDD, 
0x1F, 0xEA, 0x65, 0x0E, 0x64, 0xD3, 0x34, 0xF7, 
0x3F, 0xF6, 0x86, 0xED, 0xB4, 0xF4, 0x4B, 0xEA, 
0x82, 0xF3, 0x68, 0xEA, 0x75, 0xF3, 0x09, 0xF9, 
0x43, 0xD2, 0xFB, 0x0B, 0xCC, 0xEA, 0x4B, 0xF1, 
0x16, 0x06, 0xB9, 0xEE, 0xD9, 0x01, 0xF3, 0xE7, 
0xF4, 0xFF, 0xE9, 0x03, 0x58, 0xFD, 0xC8, 0xE8, 
0xAA, 0x0A, 0x16, 0xF6, 0xF6, 0xFA, 0x4B, 0x09, 
0xD2, 0xF7, 0x49, 0x0D, 0x84, 0xFC, 0xDD, 0xF1, 
0x50, 0x0C, 0x83, 0x01, 0xED, 0x06, 0x24, 0x08, 
0xF7, 0xF9, 0xD9, 0x0B, 0x65, 0xFB, 0x66, 0xFA, 
0x9C, 0xFF, 0x3F, 0xEA, 0x03, 0x02, 0x84, 0x0E, 
0xB1, 0xE6, 0xE7, 0x04, 0x8C, 0x0A, 0x11, 0x01, 
0xE1, 0xFD, 0xAD, 0xFD, 0x81, 0x15, 0x2E, 0x17, 
0x57, 0x09, 0x17, 0x1F, 0x61, 0x19, 0x63, 0x10, 
0x42, 0x02, 0x9B, 0x07, 0x7A, 0x07, 0x4E, 0xEF, 
0x02, 0x0C, 0xE0, 0x05, 0x31, 0x00, 0x81, 0x01, 
0x01, 0x10, 0x6D, 0x0E, 0x2A, 0x0B, 0x72, 0x08, 
0xCA, 0x0D, 0xB4, 0xF9, 0x0D, 0x0A, 0x75, 0x11, 
0x26, 0xF2, 0x5B, 0x01, 0xA2, 0xFE, 0xF4, 0x03, 
0x67, 0xF8, 0x10, 0xFC, 0x4B, 0x13, 0x93, 0x12, 
0xDA, 0x06, 0xBA, 0x16, 0x2D, 0x1E, 0x71, 0x14, 
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
