DigiTorus86/ESP32-R4ge-Pro/ArduinoIDE/esp32-r4ge-pro-drummer/Kit01_snare_wav.h

/* Include file for 8-bit PCM audio data 
 * Original filename: Kit01_snare.wav
 * Samples: 11316
 */

const PROGMEM uint8_t Kit01_snare_wav[11316] = {
0x52, 0x49, 0x46, 0x46, 0x2C, 0x2C, 0x00, 0x00, 
0x57, 0x41, 0x56, 0x45, 0x66, 0x6D, 0x74, 0x20, 
0x10, 0x00, 0x00, 0x00, 0x01, 0x00, 0x01, 0x00, 
0x22, 0x56, 0x00, 0x00, 0x44, 0xAC, 0x00, 0x00, 
0x02, 0x00, 0x10, 0x00, 0x64, 0x61, 0x74, 0x61, 
0x08, 0x2C, 0x00, 0x00, 0xC2, 0x00, 0xD6, 0xFE, 
0x75, 0x03, 0xC0, 0xF2, 0x54, 0xD5, 0xB6, 0xD2, 
0x52, 0xBE, 0xE8, 0xA9, 0xE7, 0x9F, 0x33, 0x9F, 
0x9B, 0x9E, 0xA4, 0x9B, 0x71, 0x9E, 0x76, 0x9E, 
0xB6, 0xA0, 0x60, 0xA0, 0x4E, 0xA0, 0x0A, 0xA1, 
0xA8, 0xA7, 0x4F, 0xAA, 0x6C, 0xB0, 0xEA, 0xB9, 
0x6C, 0xC2, 0x77, 0xCD, 0xA7, 0xD6, 0x48, 0xDF, 
0xCB, 0xE5, 0xA8, 0xEC, 0xA7, 0xF0, 0x01, 0xF3, 
0x9E, 0x00, 0x28, 0x0C, 0x2A, 0x0C, 0x7E, 0x15, 
0x6B, 0x2A, 0x1B, 0x35, 0x75, 0x2B, 0x3B, 0x1D, 
0x91, 0x17, 0xEA, 0x1D, 0x8D, 0x30, 0x2F, 0x49, 
0xAE, 0x5B, 0x20, 0x64, 0x83, 0x68, 0xC4, 0x6E, 
0xC7, 0x6A, 0x01, 0x61, 0x21, 0x5E, 0x6A, 0x61, 
0xD4, 0x5D, 0xFA, 0x52, 0x98, 0x4D, 0xC9, 0x4D, 
0x1B, 0x52, 0x7F, 0x5A, 0x21, 0x67, 0x18, 0x72, 
0xC3, 0x7C, 0xFF, 0x7F, 0xB5, 0x7F, 0xFC, 0x7F, 
0xCB, 0x7F, 0xFE, 0x7F, 0xCD, 0x7F, 0xFF, 0x7F, 
0xB7, 0x7F, 0xFE, 0x7F, 0x6D, 0x7F, 0xE9, 0x7F, 
0x09, 0x78, 0xDE, 0x6A, 0xB9, 0x5E, 0x71, 0x50, 
0x90, 0x40, 0x2D, 0x2E, 0xBF, 0x1B, 0xA5, 0x0B, 
0xBD, 0x01, 0x85, 0x00, 0xCB, 0x04, 0x2A, 0x07, 
0xE0, 0x03, 0x0D, 0xFE, 0x6F, 0xF8, 0xD0, 0xF1, 
0x3A, 0xE8, 0x07, 0xDF, 0xD4, 0xDC, 0xDE, 0xE0, 
0x7E, 0xE1, 0xCF, 0xD9, 0x3F, 0xD2, 0xC1, 0xD0, 
0xED, 0xCF, 0xF3, 0xCB, 0x3A, 0xC8, 0x8F, 0xC9, 
0x0E, 0xCC, 0x62, 0xCB, 0xAD, 0xC9, 0x3A, 0xCA, 
0x44, 0xCB, 0xE6, 0xCB, 0x71, 0xCB, 0xC2, 0xC7, 
0xD0, 0xC0, 0x9F, 0xB8, 0xC2, 0xB4, 0x4D, 0xB2, 
0x80, 0xAE, 0x6F, 0xAC, 0x6E, 0xAD, 0x61, 0xB0, 
0xA0, 0xB2, 0xA0, 0xB1, 0xD4, 0xAD, 0x1D, 0xAC, 
0x38, 0xAC, 0x21, 0xA8, 0x98, 0x9F, 0x79, 0x98, 
0x78, 0x96, 0x3F, 0x98, 0xEA, 0x98, 0x5A, 0x99, 
0xF8, 0x9A, 0x68, 0x9C, 0x93, 0x9C, 0xBC, 0x9E, 
0xF9, 0xA3, 0x78, 0xA9, 0x88, 0xB1, 0x72, 0xB9, 
0xB8, 0xBB, 0xF5, 0xB8, 0x62, 0xB4, 0x46, 0xAF, 
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
