DigiTorus86/ESP32-R4ge-Pro/ArduinoIDE/esp32-r4ge-pro-drummer/Title.h

/* Image include file for RGB565 bitmap 
 * Original filename: DrummerBoy2.png
 * Width: 214 * Height: 26
 */

const PROGMEM uint16_t drummer_title[5564] = {
0x000000, 0x000000, 0x000000, 0x000000, 0x000000, 0x0042C1, 0x007D04, 0x008544, // 8 pixels
0x008544, 0x008544, 0x008544, 0x008544, 0x008544, 0x008544, 0x008544, 0x007D04, // 16 pixels
0x006C43, 0x0042A1, 0x000000, 0x000000, 0x000000, 0x000000, 0x000000, 0x000000, // 24 pixels
0x000000, 0x000000, 0x000000, 0x000000, 0x000000, 0x000000, 0x000000, 0x000000, // 32 pixels
0x000000, 0x000000, 0x000000, 0x000000, 0x000000, 0x000000, 0x000000, 0x000000, // 40 pixels
0x000000, 0x000000, 0x000000, 0x000000, 0x000000, 0x000000, 0x000000, 0x000000, // 48 pixels
0x000000, 0x000000, 0x000000, 0x000000, 0x000000, 0x000000, 0x000000, 0x000000, // 56 pixels
0x000000, 0x000000, 0x000000, 0x000000, 0x000000, 0x000000, 0x000000, 0x000000, // 64 pixels
0x000000, 0x000000, 0x000000, 0x000000, 0x000000, 0x000000, 0x000000, 0x000000, // 72 pixels
0x000000, 0x000000, 0x000000, 0x000000, 0x000000, 0x000000, 0x000000, 0x000000, // 80 pixels
0x000000, 0x000000, 0x000000, 0x000000, 0x000000, 0x000000, 0x000000, 0x000000, // 88 pixels
0x000000, 0x000000, 0x000000, 0x000000, 0x000000, 0x000000, 0x000000, 0x000000, // 96 pixels
0x000000, 0x000000, 0x000000, 0x000000, 0x000000, 0x000000, 0x000000, 0x000000, // 104 pixels
0x000000, 0x000000, 0x000000, 0x000000, 0x000000, 0x000000, 0x000000, 0x000000, // 112 pixels
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
0x003A81, 0x003A81, 0x003A81, 0x003A81, 0x003A81, 0x003A41, 0x001920, 0x000000, // 5552 pixels
0x000000, 0x000000, 0x000000, 0x000000, 0x000000, 0x000000, 0x000000, 0x000000, // 5560 pixels
0x000000, 0x000000, 0x000000, 0x000000, };
