DigiTorus86/ESP32-R4ge-Pro/PlatformIO/esp32-r4ge-pro-prong/include/Bounce_wav.h

/* Include file for 8-bit PCM audio data 
 * Original filename: bounce1.wav
 * Samples: 4524
 */

#define BOUNCE_LENGTH 4524

const PROGMEM uint8_t bounce1_wav[4524] = {
0x52, 0x49, 0x46, 0x46, 0xA4, 0x11, 0x00, 0x00, 
0x57, 0x41, 0x56, 0x45, 0x66, 0x6D, 0x74, 0x20, 
0x10, 0x00, 0x00, 0x00, 0x01, 0x00, 0x01, 0x00, 
0x22, 0x56, 0x00, 0x00, 0x44, 0xAC, 0x00, 0x00, 
0x02, 0x00, 0x10, 0x00, 0x64, 0x61, 0x74, 0x61, 
0x80, 0x11, 0x00, 0x00, 0x7A, 0x00, 0x66, 0x00, 
0x54, 0x00, 0x55, 0x00, 0x0C, 0x00, 0x78, 0xFF, 
0x9F, 0xFE, 0x30, 0xFE, 0x95, 0xFE, 0x45, 0x00, 
0x88, 0x07, 0x50, 0x2B, 0x8D, 0x69, 0x6D, 0x7E, 
0xFF, 0x7F, 0x4D, 0x7D, 0xE9, 0x52, 0xDF, 0xFE, 
0x3B, 0xAE, 0x03, 0x85, 0x01, 0x80, 0x00, 0x80, 
0x88, 0x81, 0x64, 0xA3, 0x41, 0xFE, 0xE9, 0x4F, 
0x61, 0x7C, 0xFE, 0x7F, 0xFF, 0x7F, 0xCC, 0x69, 
0xFB, 0x23, 0x9E, 0xD4, 0xCC, 0x93, 0xBB, 0x80, 
0x00, 0x80, 0x01, 0x80, 0xE6, 0x95, 0x88, 0xD9, 
0x6A, 0x2F, 0x39, 0x6D, 0xC9, 0x7F, 0xFF, 0x7F, 
0x66, 0x78, 0x45, 0x44, 0xCB, 0xF3, 0x85, 0xAB, 
0xC3, 0x85, 0x00, 0x80, 0x02, 0x80, 0x31, 0x89, 
0x98, 0xC3, 0x3D, 0x15, 0x9C, 0x59, 0x66, 0x7A, 
0xFF, 0x7F, 0x52, 0x7D, 0xA7, 0x58, 0x3C, 0x16, 
0x0B, 0xCB, 0x24, 0x95, 0x00, 0x82, 0x00, 0x80, 
0x94, 0x84, 0xF4, 0xAD, 0xF4, 0xF2, 0x43, 0x3B, 
0xD4, 0x6E, 0x7A, 0x7F, 0x60, 0x7F, 0x58, 0x6B, 
0x70, 0x30, 0xCC, 0xE9, 0xE2, 0xAB, 0x6A, 0x89, 
0x50, 0x80, 0xA1, 0x82, 0x37, 0x9B, 0x34, 0xD8, 
0x2A, 0x1F, 0x94, 0x5B, 0x95, 0x78, 0x03, 0x7F, 
0x79, 0x75, 0xBA, 0x47, 0x55, 0x09, 0x1A, 0xC9, 
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
0xC2, 0x61, 0xBB, 0x5F, 0x5F, 0x47, 0xD4, 0x16, 
0x0B, 0xE2, 0x58, 0xBB, 0x9A, 0xAB, 0xEE, 0xA6, 
0x4A, 0xB1, 0xE4, 0xD5, 0xB2, 0x09, 0x26, 0x3C, 
0xF9, 0x51, 0xD8, 0x57, 0x44, 0x54, 0x42, 0x32, 
0x88, 0xFE, 0x7E, 0xCD, 0x72, 0xB2, 0xB7, 0xA6, 
0xEA, 0xA5, 0x8A, 0xBB, 0x3F, 0xE8, 0x6E, 0x1F, 
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
