DigiTorus86/ESP32-R4ge-Pro/PlatformIO/esp32-r4ge-pro-prong/include/Score_wav.h

/* Include file for 8-bit PCM audio data 
 * Original filename: score.wav
 * Samples: 19560
 */

const PROGMEM uint8_t score_wav[19560] = {
0x52, 0x49, 0x46, 0x46, 0x60, 0x4C, 0x00, 0x00, 
0x57, 0x41, 0x56, 0x45, 0x66, 0x6D, 0x74, 0x20, 
0x10, 0x00, 0x00, 0x00, 0x01, 0x00, 0x01, 0x00, 
0x22, 0x56, 0x00, 0x00, 0x44, 0xAC, 0x00, 0x00, 
0x02, 0x00, 0x10, 0x00, 0x64, 0x61, 0x74, 0x61, 
0x3C, 0x4C, 0x00, 0x00, 0x58, 0xFA, 0x87, 0xFB, 
0xAA, 0x04, 0xC8, 0x0B, 0x54, 0x12, 0x30, 0x12, 
0x66, 0x0E, 0x6C, 0x0A, 0x7F, 0x08, 0xA8, 0x07, 
0xE4, 0x05, 0xC2, 0x02, 0x4C, 0xFF, 0x86, 0xFD, 
0xA1, 0xFD, 0x51, 0xFF, 0xCD, 0x01, 0xF9, 0x03, 
0x9A, 0x02, 0xAF, 0xFC, 0x6C, 0xF5, 0x34, 0xF1, 
0x9A, 0xF0, 0x97, 0xF0, 0x5B, 0xEF, 0xAC, 0xED, 
0x7C, 0xED, 0xC9, 0xF0, 0x1F, 0xF9, 0x26, 0x05, 
0x8D, 0x0E, 0x41, 0x0E, 0xBE, 0x03, 0x1E, 0xF6, 
0xB4, 0xEE, 0xD2, 0xF1, 0x4C, 0xFE, 0x2A, 0x0E, 
0x3F, 0x1A, 0x0F, 0x1D, 0x13, 0x18, 0x2B, 0x11, 
0xDE, 0x0D, 0x92, 0x0D, 0x3F, 0x0C, 0x83, 0x0A, 
0x6D, 0x04, 0xDB, 0xFE, 0x91, 0x02, 0xF9, 0x06, 
0xAF, 0x05, 0x33, 0x0A, 0x9C, 0x07, 0xC0, 0xF9, 
0xBB, 0xF7, 0xFB, 0xF0, 0x32, 0xF0, 0x7B, 0xF6, 
0xE2, 0xEA, 0x5C, 0xEE, 0x79, 0xEE, 0x82, 0xE7, 
0xDB, 0xF7, 0x5B, 0xF7, 0xED, 0xF9, 0x33, 0x02, 
0x6B, 0xF4, 0x4D, 0xF8, 0x39, 0xFB, 0x70, 0xF9, 
0x86, 0x03, 0xB7, 0x01, 0xF9, 0x04, 0x9E, 0x09, 
0xFE, 0x0B, 0x6F, 0x13, 0xAB, 0x13, 0xC5, 0x16, 
0x20, 0x0D, 0xF2, 0x03, 0x60, 0x06, 0x48, 0x01, 
0xA2, 0x0C, 0xB8, 0x0F, 0xAF, 0x08, 0x3B, 0x0C, 
0xDB, 0xFC, 0xE4, 0xF5, 0xC1, 0xF8, 0x16, 0xF2, 
0xB3, 0xF6, 0x7F, 0xF2, 0xD9, 0xF1, 0xFA, 0xFC, 
0xFD, 0xF0, 0x8E, 0xE3, 0xAA, 0xEB, 0x7F, 0xFA, 
0x82, 0xFB, 0x8F, 0xFB, 0xE3, 0xF4, 0x7F, 0xD9, 
0x03, 0xEA, 0x95, 0x0E, 0x09, 0x0F, 0xBF, 0x0F, 
0x2B, 0x07, 0x63, 0x01, 0x3F, 0x0D, 0x84, 0x15, 
0x9A, 0x17, 0x93, 0x01, 0xA5, 0xFD, 0x1B, 0x08, 
0xFE, 0x08, 0x94, 0x27, 0x76, 0x27, 0x0C, 0x0A, 
0x95, 0x07, 0x3B, 0x05, 0xE6, 0x06, 0xC0, 0xFF, 
0xB7, 0xFB, 0xBC, 0xF8, 0xCE, 0xDF, 0x79, 0xFA, 
0xB4, 0x12, 0x8E, 0xF1, 0x12, 0xEC, 0x28, 0xF2, 
0x1E, 0xEE, 0xE8, 0xF5, 0xF8, 0x02, 0x70, 0xF8, 
0x29, 0xD5, 0xB7, 0xDD, 0x6A, 0xF8, 0x66, 0xFD, 
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
};
